lata-mas/DFP-10/Diagramas/circuito zmpt10b.png

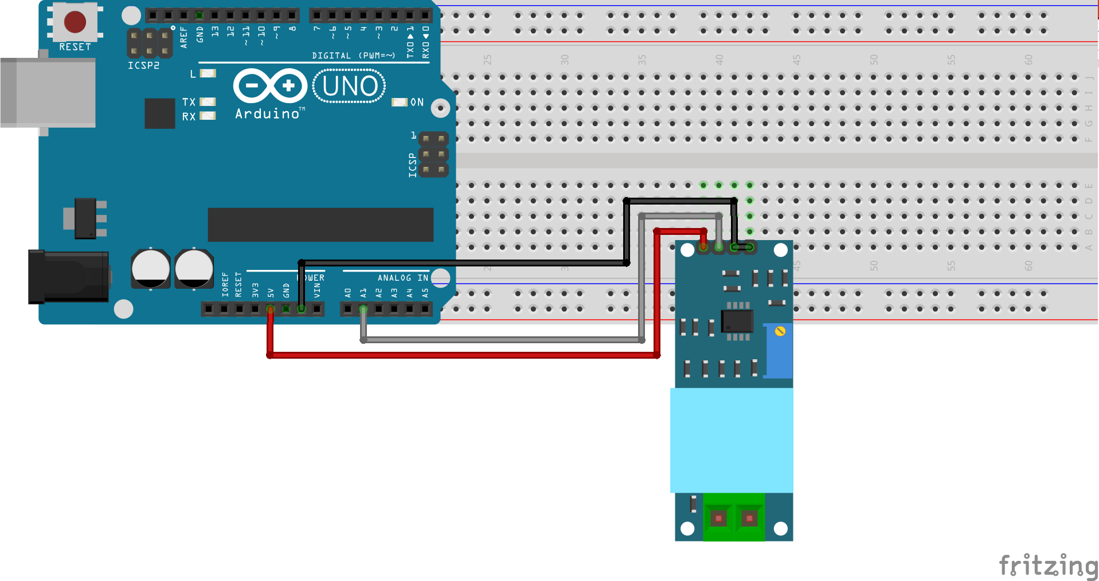
Diagramas/circuito zmpt10b.png
