lata-mas/DFP-10/Diagramas/Circuito_monofasico_PZEM-004T.jpg

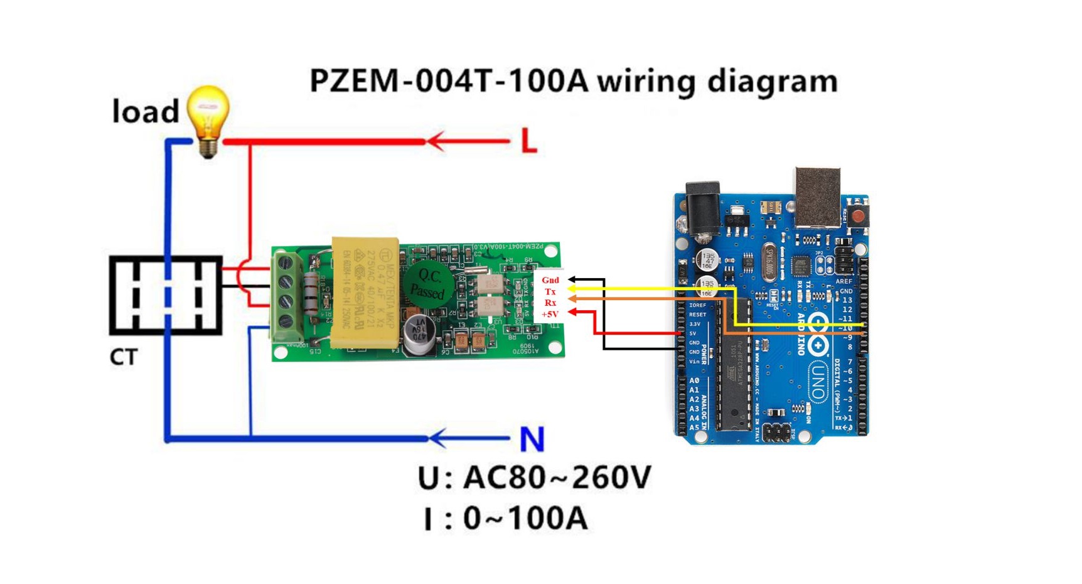
Diagramas/Circuito_monofasico_PZEM-004T.jpg
