lata-mas/DFP-10/SRC/monitor_energia_monofasico/arduino_secrets.h

#ifndef _ARDUINO_SECRETS_H_
#define _ARDUINO_SECRETS_H_

#define SECRET_SSID "IER" //IER //TOTALPLAY_9A0650
#define SECRET_PASS "acadier2014" //acadier2014 //W1D41WSC17g

#ifdef _ARDUINO_MQTT_CLIENT_H_
#define SECRET_BROKER "iot.ier.unam.mx"
#define SECRET_PORT 1883
#define SECRET_DEVID "d147d250-d24a-11eb-897a-cd1c177f68f0"
#define SECRET_TOKEN "nCsfwwiNH8JpXLmI2yuY"
#define SECRET_TOPIC "v1/devices/me/telemetry"
#endif

#ifdef ArduinoHttpClient_h
#define SECRET_SERVER "iot.ier.unam.mx"
#define SECRET_PORT 8080
#define SECRET_TOPIC "/api/v1/283aV76r6z4CIccCw6cC/telemetry"
#endif

#endif
